j8m1e/PID-Stewart-Platform/stewy-master/doc/stewduino.sch

## EAGLE design stewy-master/doc/stewduino.sch (2018-12-09, last stored version)

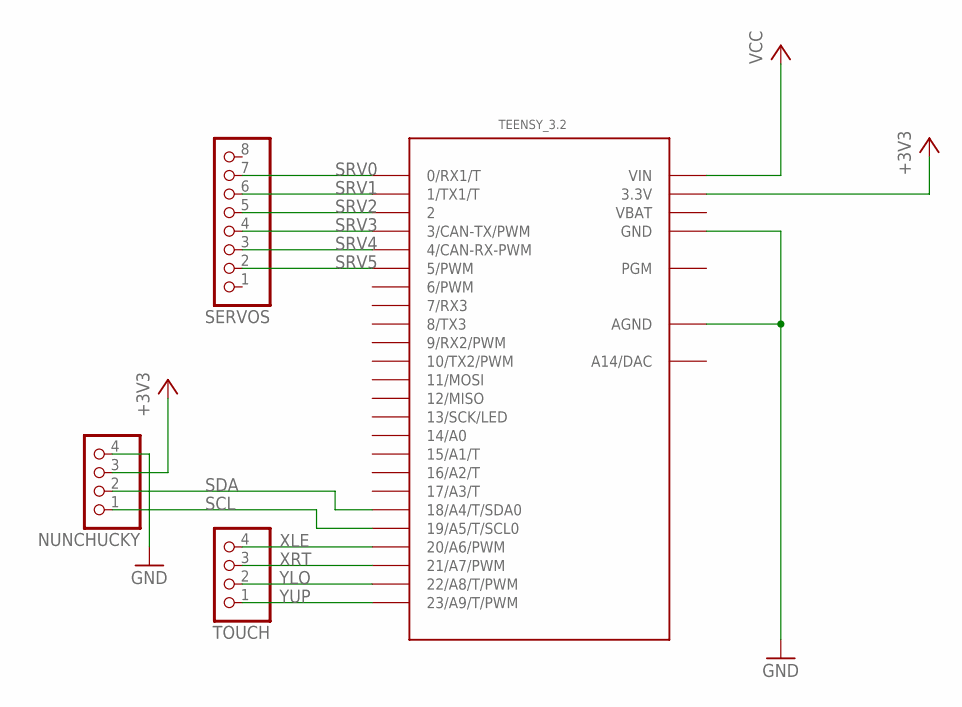
[picture p12: schematic stewduino.sch]

Parts:
NUNCHUCKY: PINHD-1X4; 1X04
SERVOS: PINHD-1X8; 1X08
TEENSY_3.2: TEENSY_3.1-3.2_OUTER_ROW; TEENSY_3.0-3.2&LC_OUTER_ROW
TOUCH: PINHD-1X4; 1X04

Connections:
+3V3: NUNCHUCKY.3, TEENSY_3.2.3.3V
GND: NUNCHUCKY.4, TEENSY_3.2.AGND, TEENSY_3.2.GND
SCL: NUNCHUCKY.1, TEENSY_3.2.19/A5 (19/A5/T/SCL0)
SDA: NUNCHUCKY.2, TEENSY_3.2.18/A4 (18/A4/T/SDA0)
SRV0: SERVOS.7, TEENSY_3.2.0 (0/RX1/T)
SRV1: SERVOS.6, TEENSY_3.2.1 (1/TX1/T)
SRV2: SERVOS.5, TEENSY_3.2.2
SRV3: SERVOS.4, TEENSY_3.2.3 (3/CAN-TX/PWM)
SRV4: SERVOS.3, TEENSY_3.2.4 (4/CAN-RX-PWM)
SRV5: SERVOS.2, TEENSY_3.2.5 (5/PWM)
VCC: TEENSY_3.2.VIN
XLE: TEENSY_3.2.20/A6 (20/A6/PWM), TOUCH.4
XRT: TEENSY_3.2.21/A7 (21/A7/PWM), TOUCH.3
YLO: TEENSY_3.2.22/A8 (22/A8/T/PWM), TOUCH.2
YUP: TEENSY_3.2.23/A9 (23/A9/T/PWM), TOUCH.1
